AiuRat/breadboard-power-qcpd/electronics/verification/README.md

<p align="center">
  <b>Русский</b> | <a href="README.en.md">English</a> | <a href="README.de.md">Deutsch</a>
</p>

# Электрический расчет и верификация инвертора -15 В

Здесь представлен подробный расчет внешней обвязки импульсного регулирующего контроллера **MC34063AG** в инвертирующем режиме работы, а также результаты его практических испытаний с помощью цифрового осциллографа.

Инвертирующий режим работы необходим для формирования стабильного отрицательного напряжения $-15\text{ В}$, используемого для двухполярного питания аналоговых узлов (операционных усилителей, компараторов) на беспаечной макетной плате.

---

## 1. Схема электрическая принципиальная узла

Теоретическая схема подключения микросхемы в инвертирующем режиме представлена ниже:

Схема обвязки MC34063

### Исходные параметры для расчета:
* Максимальное входное напряжение: $U_{\text{вх(макс)}} = 20\text{ В}$ (соответствует максимальному профилю USB Power Delivery)
* Номинальное входное напряжение: $U_{\text{вх}} = 5\text{ В}$
* Требуемое выходное напряжение: $U_{\text{вых}} = -15\text{ В}$
* Максимальный выходной ток: $I_{\text{вых}} = 100\text{ мА}$
* Допустимое напряжение пульсаций на выходе: $U_{\text{пульс(пик-пик)}} = 10\text{ мВ}$

---

## 2. Теоретический расчет компонентов обвязки

### 2.1. Определение временных интервалов и выбор частоты
Частота работы встроенного генератора задается емкостью конденсатора $C_1$ (подключен между выводом `TC` и землей). Для обеспечения компактности устройства и уменьшения габаритов дросселя выбирается высокая частота переключения.

По графику из технической документации (Datasheet) при емкости конденсатора $C_1 = 100\text{ пФ}$ выбираются следующие временные интервалы:
* Интервал проводимости выходного ключа: $t_{\text{вкл}} = 4\ \mu\text{с}$
* Интервал запирания выходного ключа: $t_{\text{выкл}} = 1\ \mu\text{с}$

<p align="center">
  График зависимости частоты от емкости
</p>
  
### 2.2. Расчет тока насыщения дросселя ($I_{\text{нас}}$)
Ток насыщения дросселя $L_1$ рассчитывается по формуле:

$$I_{\text{нас}} = 2 \cdot I_{\text{вых(макс)}} \cdot \frac{t_{\text{вкл}} + t_{\text{выкл}}}{t_{\text{выкл}}}$$

Подставляя значения:

$$I_{\text{нас}} = 2 \cdot 0{,}1 \cdot \frac{4 \cdot 10^{-6} + 1 \cdot 10^{-6}}{1 \cdot 10^{-6}} = 1\text{ А}$$

### 2.3. Расчет минимальной индуктивности дросселя ($L_{\text{мин}}$)
Минимальная индуктивность рассчитывается для наихудшего случая (при максимальном входном напряжении):

$$L_{\text{мин}} = \left( \frac{U_{\text{вх(макс)}} - U_{\text{вых(нас)}}}{I_{\text{нас}}} \right) \cdot t_{\text{вкл(макс)}}$$

Где $U_{\text{вых(нас)}}$ — напряжение насыщения выходного транзистора внутри микросхемы при токе $1\text{ А}$. Согласно справочному графику из даташита, это значение составляет $1{,}65\text{ В}$:

<p align="center">
  График напряжения насыщения
</p>
  
Вычисляем значение индуктивности:

$$L_{\text{мин}} = \left( \frac{20 - 1{,}65}{1} \right) \cdot 4 \cdot 10^{-6} \approx 73\ \mu\text{Гн}\ (73\text{ мкГн})$$

*Выбор компонента:* С целью повышения надежности, снижения пульсаций и обеспечения непрерывного режима работы выбран дроссель стандартного номинала **220 мкГн** (модель *SPQ105-560M* / *B82464G4224M*).

### 2.4. Расчет токоограничительного резистора ($R_3$)
Резистор $R_3$ (подключен к выводу `IPK`) служит для защиты микросхемы от перегрузки по току:

$$R_3 = \frac{0{,}3}{I_{\text{нас}}} = \frac{0{,}3}{1} = 0{,}3\ \Omega\ (0{,}3\text{ Ом})$$

*Выбор номинала:* Выбран стандартный низкоомный резистор номиналом **0,22 Ом** (или 0,3 Ом).

### 2.5. Расчет сглаживающего конденсатора ($C_3$)
Емкость выходного сглаживающего конденсатора $C_3$ (в исходных формулах дипломной работы обозначен как $C_1$):

$$C_3 = \frac{I_{\text{вых}} \cdot t_{\text{вкл}}}{U_{\text{пульс(пик-пик)}}} = \frac{0{,}1 \cdot 4 \cdot 10^{-6}}{10 \cdot 10^{-3}} = 40\ \mu\text{Ф}\ (40\text{ мкФ})$$

*Выбор компонента:* Из стандартного ряда E12 выбран танталовый конденсатор емкостью **47 мкФ** (тип CASE-D).

### 2.6. Теоретический расчет делителя обратной связи ($R_1$, $R_4$)
Для стабилизации выходного напряжения на уровне $-15\text{ В}$ используется встроенный компаратор с опорным напряжением $1{,}25\text{ В}$. Теоретический расчет при токе делителя $I_{\text{д}} = 1\text{ мА}$ дает формулы:

$$R_1 = \frac{|U_{\text{вых}}| - 1{,}25}{I_{\text{д}}} = \frac{15 - 1{,}25}{0{,}001} = 13750\ \Omega\ (13{,}75\text{ кОм})$$

$$R_4 = \frac{1{,}25}{I_{\text{д}}} = \frac{1{,}25}{0{,}001} = 1250\ \Omega\ (1{,}25\text{ кОм})$$

*Теоретический выбор по ряду E24:* $R_1 = 13\text{ кОм}$, $R_4 = 1{,}2\text{ кОм}$.

---

## 3. Практическая отладка макета (Важно!)

При сборке и первом запуске физического макета было обнаружено, что теоретические номиналы обратной связи и управляющих цепей требуют корректировки из-за реальных падений напряжений на элементах и паразитных параметров. 

### Произведенные изменения в финальной версии (v5):
1. **Делитель обратной связи MC34063:** Для получения точного и стабильного уровня $-15\text{ В}$ на физической плате экспериментальным путем был установлен делитель из резисторов **$R_4 = 910\text{ Ом}$** и **$R_1 = 10\text{ кОм}$** (с последовательным подстроечным элементом $R_5 = 750\text{ Ом}$). Это компенсировало падение напряжения на выпрямительном диоде Шоттки $VD_1$ и обеспечило стабильную генерацию отрицательного плеча.
2. **Резисторы подтяжки CH224K:** В цепях конфигурации `CFG1–CFG3` триггера быстрой зарядки резисторы были изменены с **1 кОм на 10 кОм**. Слишком малый номинал в 1 кОм мешал микросхеме корректно переключать логические уровни для запроса нужного профиля напряжения от сетевого адаптера.

---

## 4. Результаты физических измерений (Верификация)

Для подтверждения стабильности работы схемы была проведена осциллографическая регистрация сигналов в ключевых точках устройства.

### 4.1. Форма сигнала на частотозадающем конденсаторе $C_1$
Реальная рабочая частота встроенного генератора составила **97,5 кГц** (при расчетном максимуме 100 кГц для данной микросхемы). Форма напряжения имеет классический пилообразный характер без искажений, что подтверждает стабильность внутреннего осциллятора.

<p align="center">
  Осциллограмма C1
</p>

### 4.2. Форма сигнала на дросселе $L_1$
Измерение в точке коммутации ключа (вывод `SWE` / анод диода `VD1`) подтверждает работу преобразователя в расчетном импульсном режиме. Интервал проводимости составляет $4\ \mu\text{с}$, интервал запирания — $1\ \mu\text{с}$, что полностью согласуется с расчетными параметрами времени включения/выключения. Присутствующие высокочастотные колебания (звон) при переключении находятся в пределах допустимых норм для выбранного диода Шоттки $15MQ040N$

<p align="center">
  Осциллограмма L1
</p>

---

## 5. Сравнение расчетных и экспериментальных данных

| Параметр | Расчетное значение | Фактическое (макет) | Статус верификации |
| :--- | :---: | :---: | :--- |
| **Выходное напряжение ($U_{\text{вых}}$)** | -14,57 В | -15,02 В | **Пройдено** (точность ≈ 3%) |
| **Рабочая частота ($f$)** | 100 кГц (макс) | 97,5 кГц | **Пройдено** (оптимально для MC34063) |
| **Время проводимости ($t_{\text{вкл}}$)** | 4,0 мкс | 4,0 мкс | **Пройдено** (полное соответствие) |
| **Время запирания ($t_{\text{выкл}}$)** | 1,0 мкс | 1,0 мкс | **Пройдено** (полное соответствие) |
| **Амплитуда пульсаций (пик-пик)** | < 100 мВ | ≈ 85 мВ | **Пройдено** (с запасом для макеток) |
